PatternAgents/Hula_Poppy/Hula_Poppy/eagleUp/eagleUp_hula_poppy_board_top.jpg

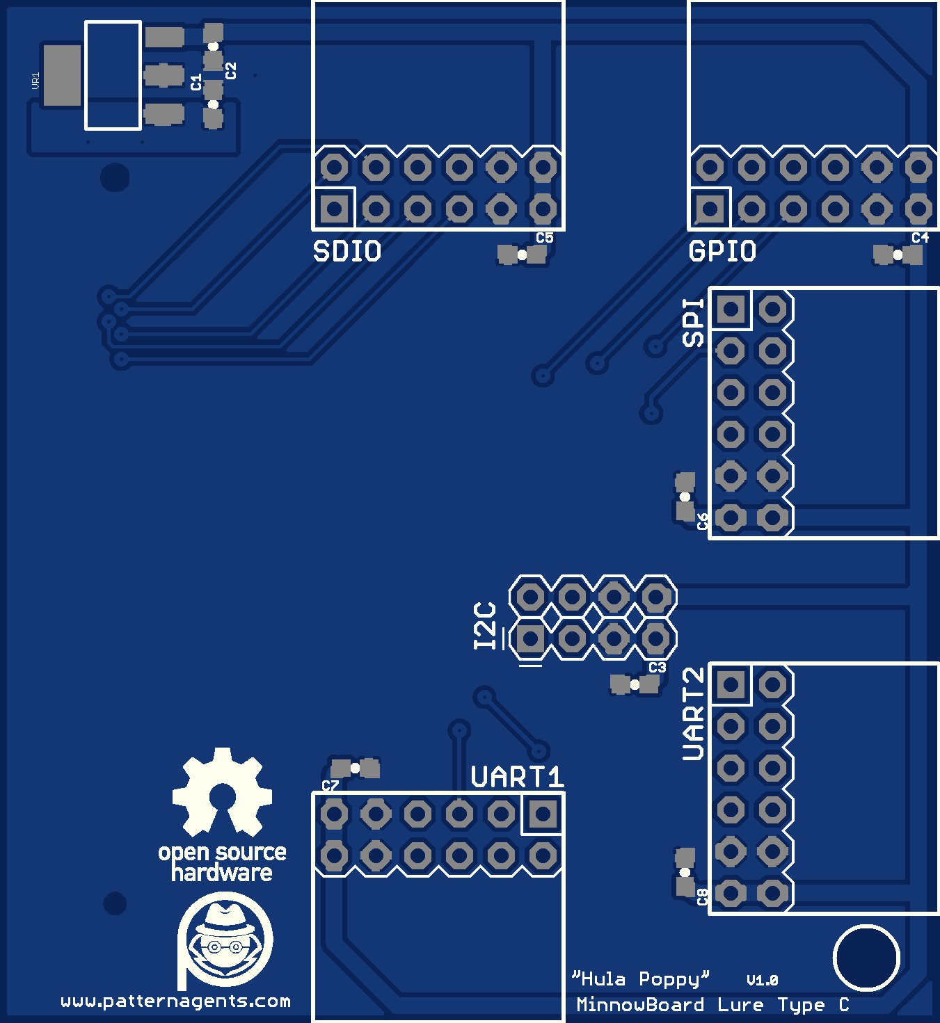
Hula_Poppy/eagleUp/eagleUp_hula_poppy_board_top.jpg
