PatternAgents/Hula_Poppy/Hula_Poppy/eagleUp/eagleUp_hula_poppy_bottom.png

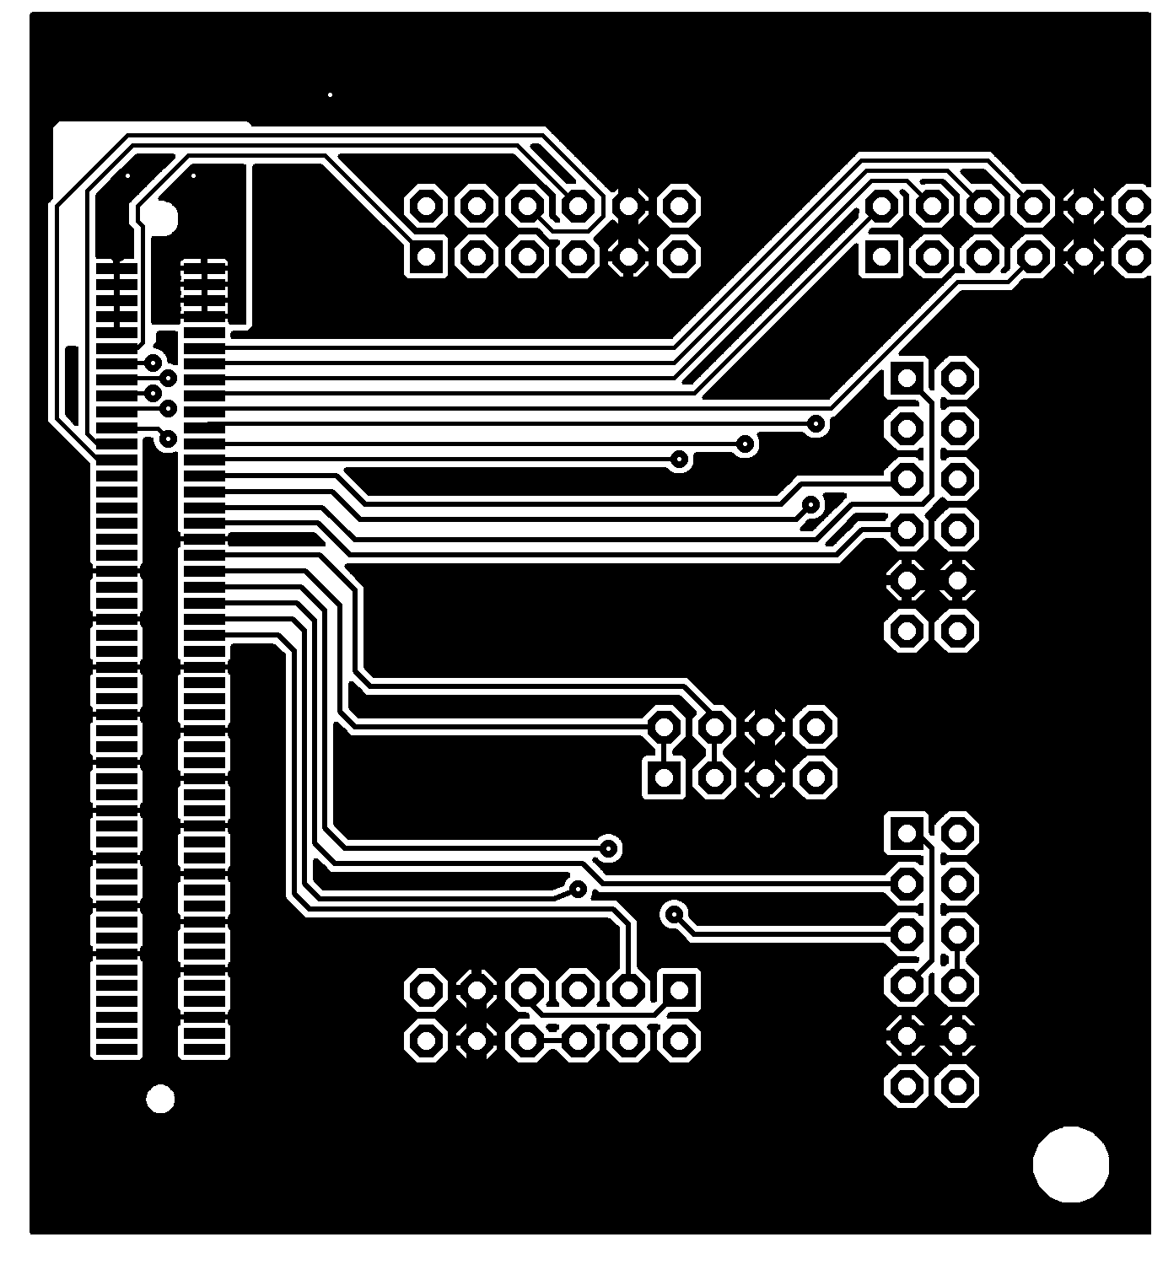
Hula_Poppy/eagleUp/eagleUp_hula_poppy_bottom.png
