PatternAgents/Hula_Poppy/Hula_Poppy/eagleUp/eagleUp_hula_poppy_imagesize.png

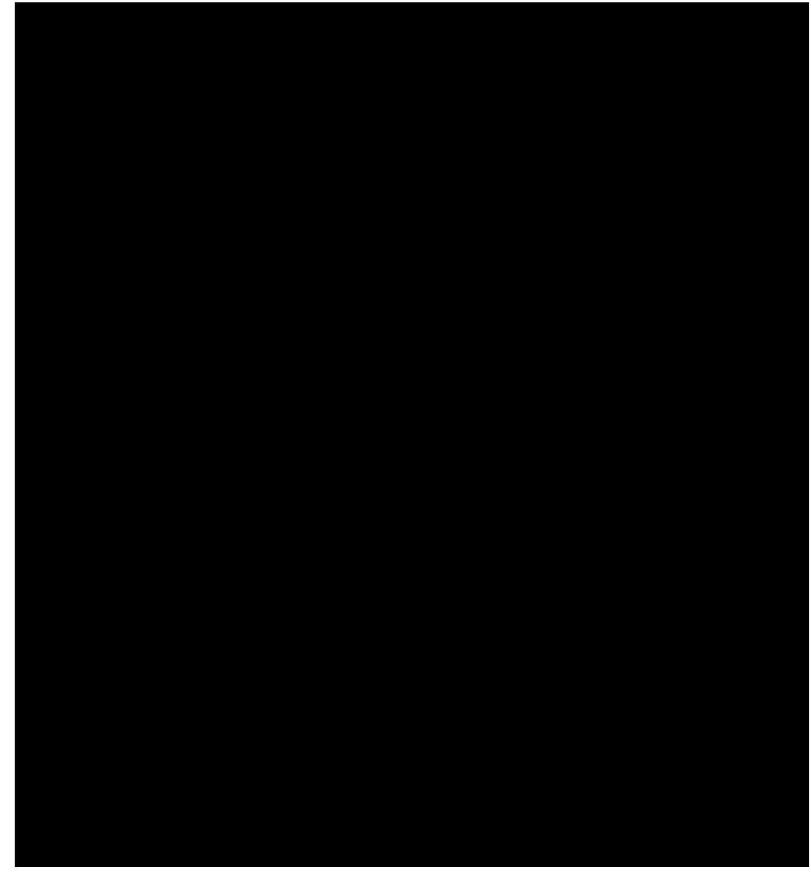
Hula_Poppy/eagleUp/eagleUp_hula_poppy_imagesize.png
