PatternAgents/Hula_Poppy/Hula_Poppy/eagleUp/eagleUp_hula_poppy_outline.png

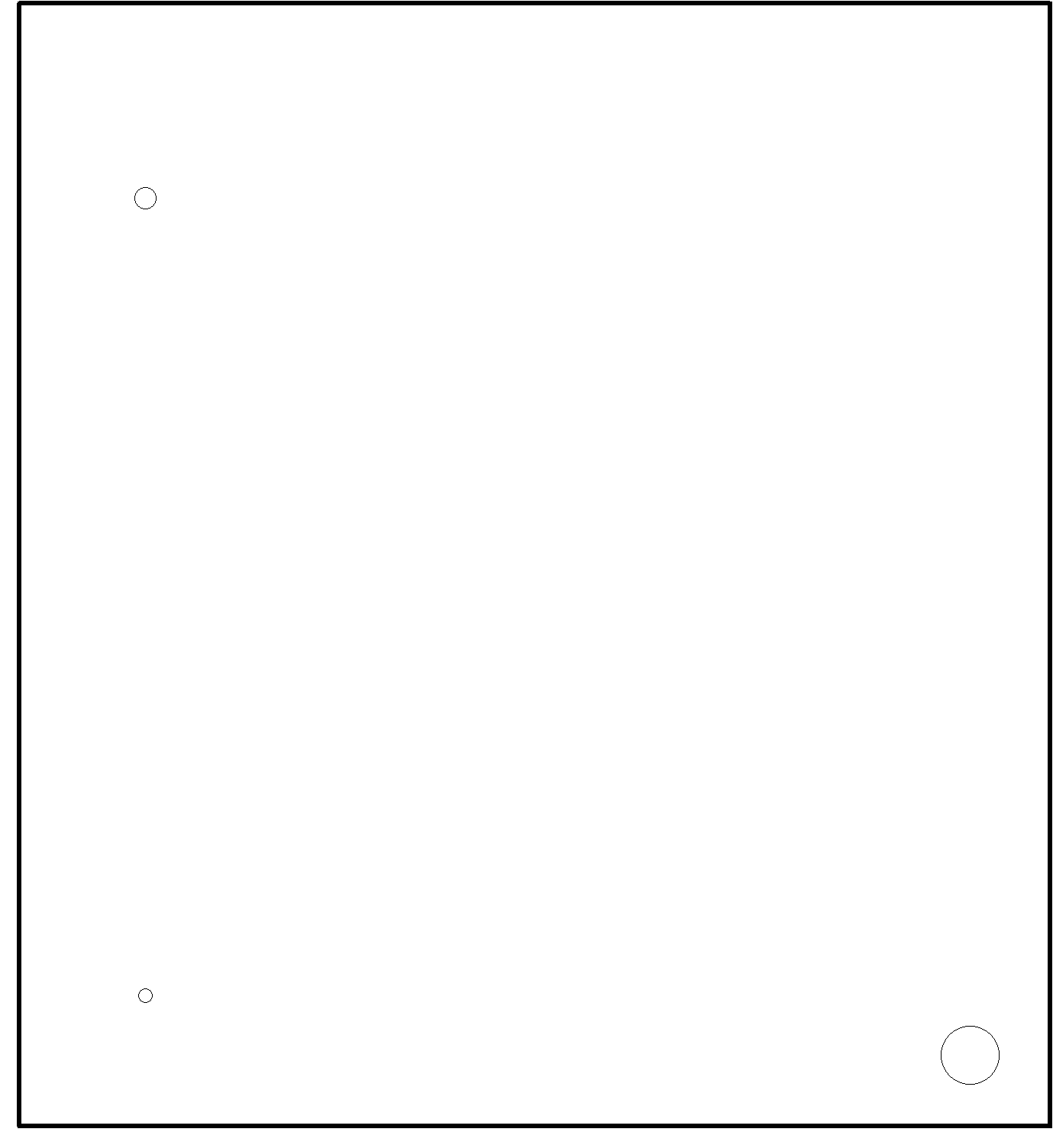
Hula_Poppy/eagleUp/eagleUp_hula_poppy_outline.png
