PatternAgents/Hula_Poppy/Hula_Poppy/eagleUp/eagleUp_hula_poppy_top.png

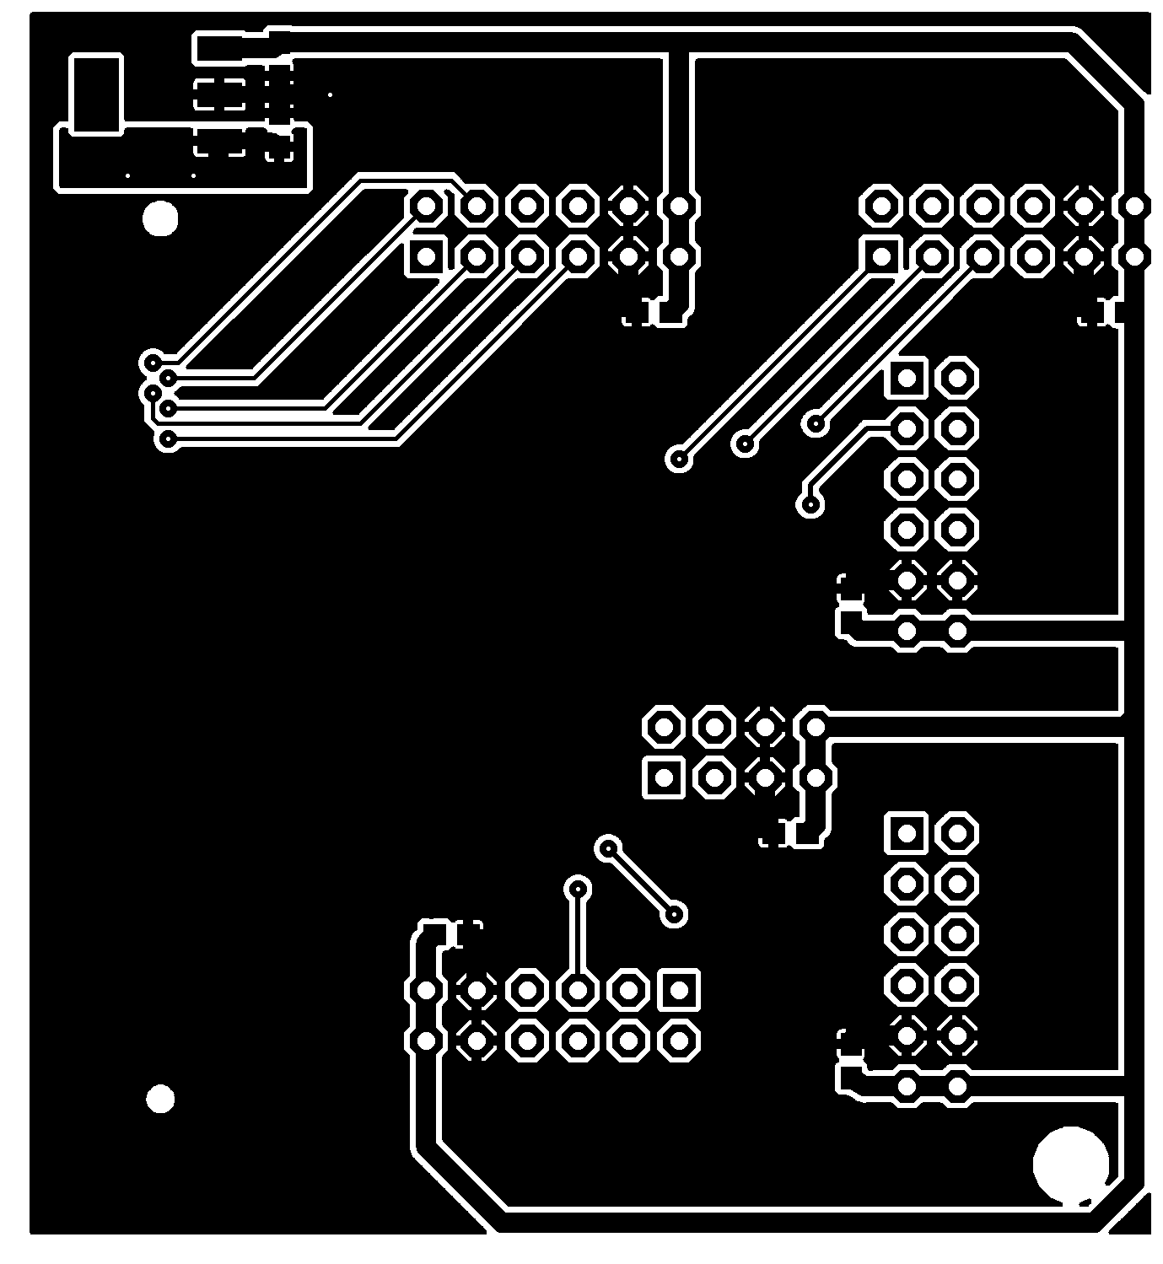
Hula_Poppy/eagleUp/eagleUp_hula_poppy_top.png
