PatternAgents/Hula_Poppy/Hula_Poppy/eagleUp/eagleUp_hula_poppy_top_mask.png

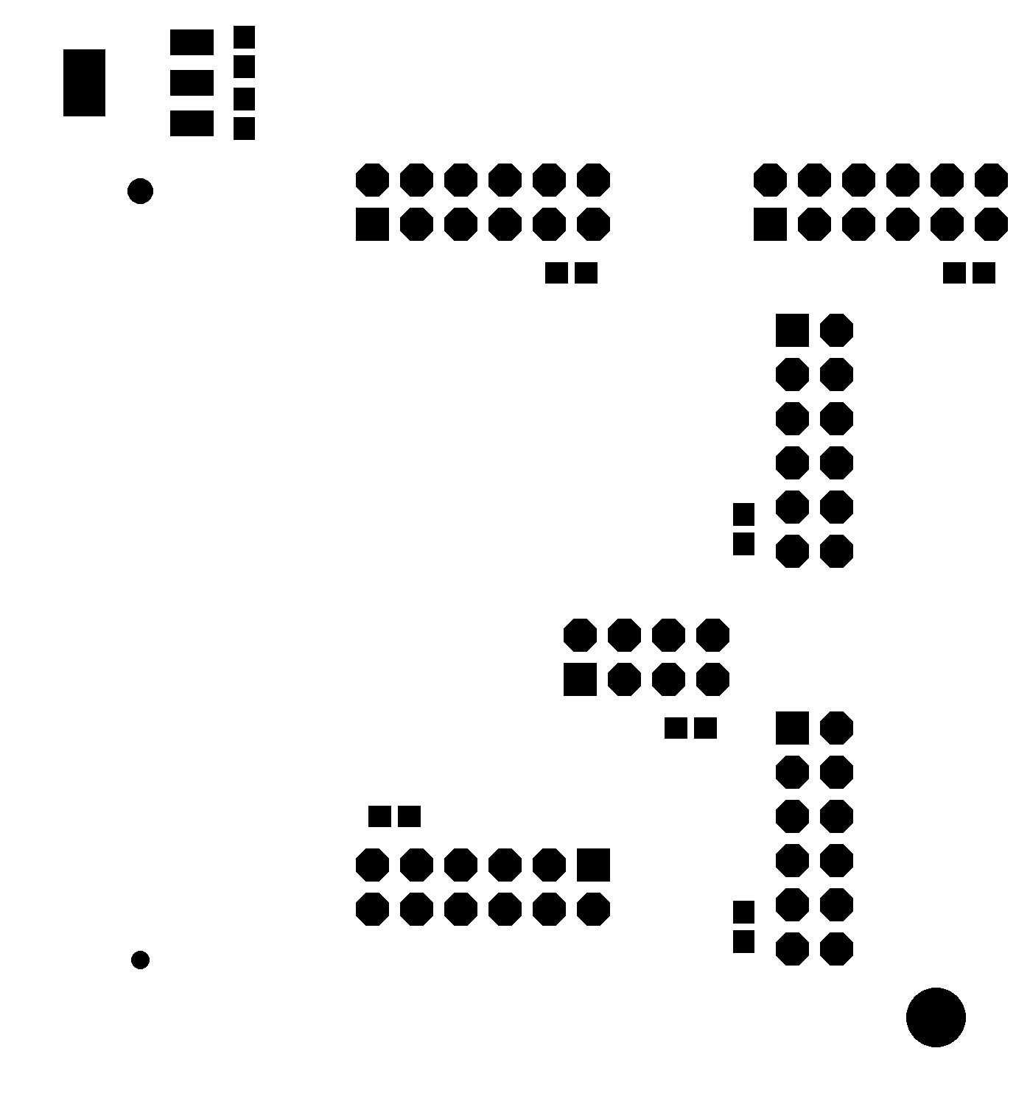
Hula_Poppy/eagleUp/eagleUp_hula_poppy_top_mask.png
