PatternAgents/Hula_Poppy/Hula_Poppy/images/Hula_Poppy.png

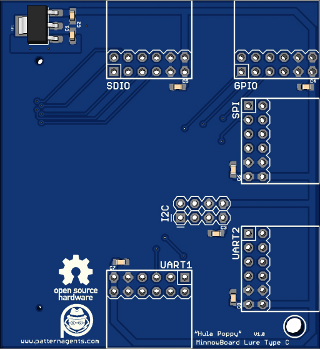
Hula_Poppy/images/Hula_Poppy.png
