PatternAgents/Hula_Poppy/Hula_Poppy/images/Hula_Poppy_iso.png

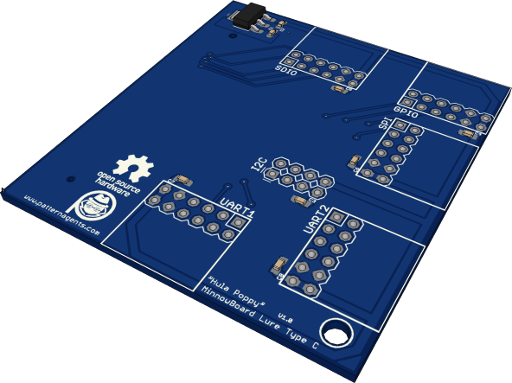
Hula_Poppy/images/Hula_Poppy_iso.png
